kmani314/ATMega32u4-HID-Keyboard/include/matrix.h

#ifndef MATRIX_H
#define MATRIX_H

#include <stdbool.h>

#define NUM_ROWS 4
#define NUM_COLS 12
#define B_OFFSET 4  // PORTB does not start at 0, 0-3 is used for ICSP

void matrix_init();
void do_matrix_scan();
#endif
